HeikkiHietala/queue_sensor/IMG_20190201_143448.jpg

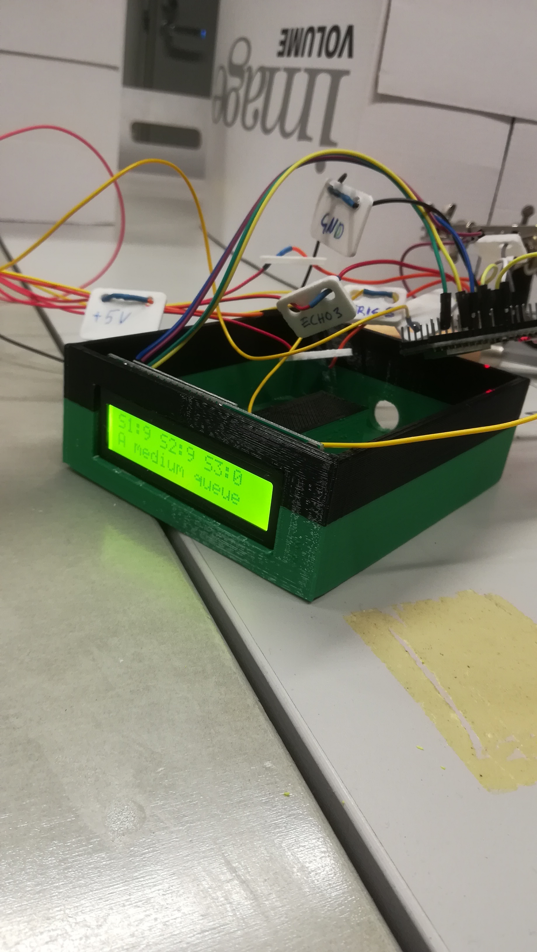
IMG_20190201_143448.jpg
