HeikkiHietala/queue_sensor/IMG_20190205_164959_709.jpg

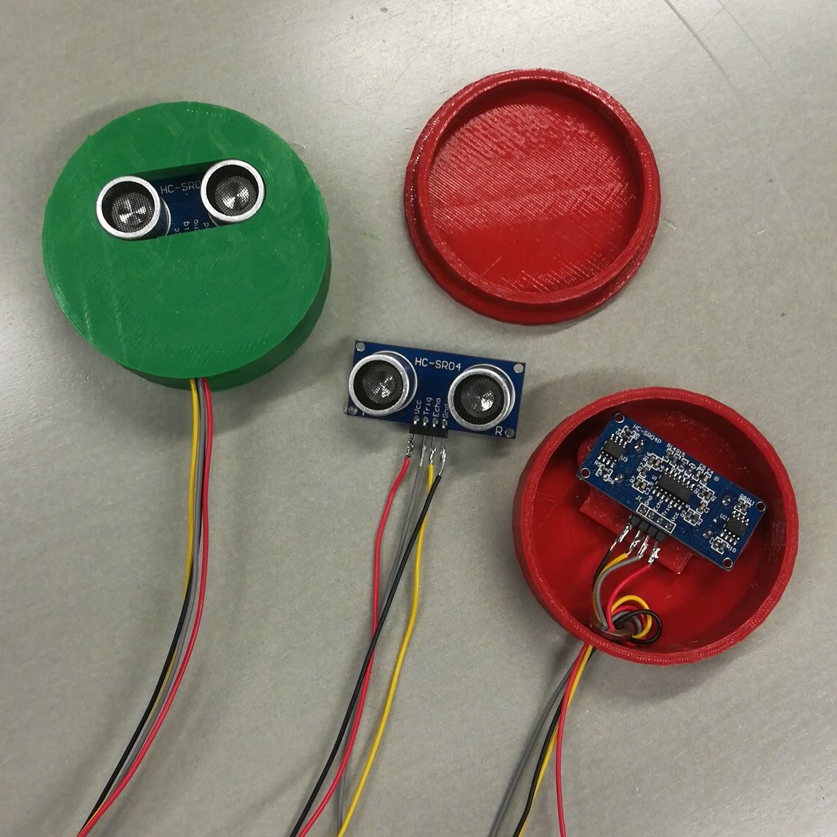
IMG_20190205_164959_709.jpg
