HeikkiHietala/queue_sensor/IMG_20190319_101405_016.jpg

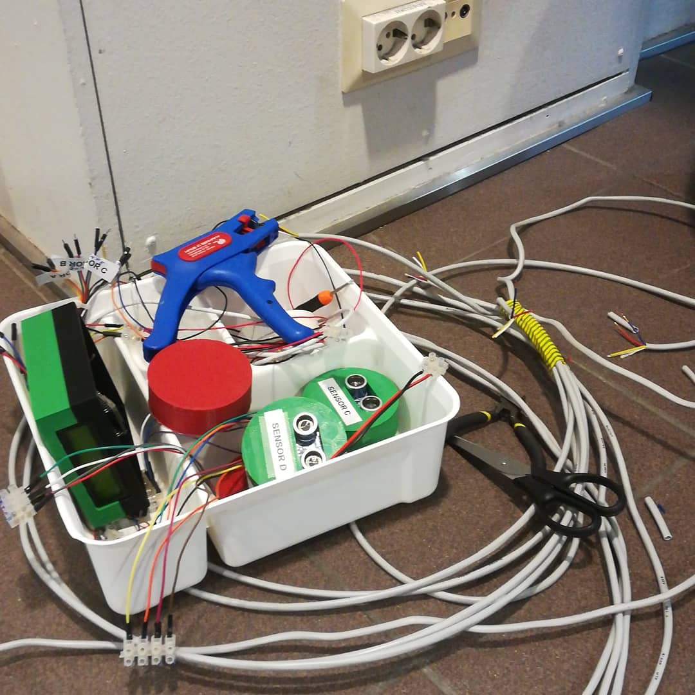
IMG_20190319_101405_016.jpg
